ricardomv/temp-humidity-mikrobus/temp-humid.X/src/periph/rtcc.c

/**
  RTCC Generated Driver API Header File

  @Company:
    Microchip Technology Inc.

  @File Name:
    rtcc.c

  @Summary:
    This is the generated header file for the RTCC driver using PIC24 / dsPIC33 / PIC32MM MCUs

  @Description:
    This header file provides APIs for driver for RTCC.
    Generation Information :
        Product Revision  :  PIC24 / dsPIC33 / PIC32MM MCUs - pic24-dspic-pic32mm : 1.75.1
        Device            :  PIC24FJ1024GB610
    The generated drivers are tested against the following:
        Compiler          :  XC16 v1.35
        MPLAB 	          :  MPLAB X v5.05
*/

/*
    (c) 2016 Microchip Technology Inc. and its subsidiaries. You may use this
    software and any derivatives exclusively with Microchip products.

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
    IN NO EVENT WILL MICROCHIP BE LIABLE FOR ANY INDIRECT, SPECIAL, PUNITIVE,
    INCIDENTAL OR CONSEQUENTIAL LOSS, DAMAGE, COST OR EXPENSE OF ANY KIND
    WHATSOEVER RELATED TO THE SOFTWARE, HOWEVER CAUSED, EVEN IF MICROCHIP HAS
    BEEN ADVISED OF THE POSSIBILITY OR THE DAMAGES ARE FORESEEABLE. TO THE
    FULLEST EXTENT ALLOWED BY LAW, MICROCHIP'S TOTAL LIABILITY ON ALL CLAIMS IN
    ANY WAY RELATED TO THIS SOFTWARE WILL NOT EXCEED THE AMOUNT OF FEES, IF ANY,
    THAT YOU HAVE PAID DIRECTLY TO MICROCHIP FOR THIS SOFTWARE.

    MICROCHIP PROVIDES THIS SOFTWARE CONDITIONALLY UPON YOUR ACCEPTANCE OF THESE
    TERMS.
*/


/**
 Section: Included Files
*/

#include <xc.h>
#include "rtcc.h"

/**
// Section: Static function
*/

static void RTCC_Lock(void);
static bool rtccTimeInitialized;
static bool RTCCTimeInitialized(void);
static uint8_t ConvertHexToBCD(uint8_t hexvalue);
static uint8_t ConvertBCDToHex(uint8_t bcdvalue);

void __attribute__ ((weak)) rtcc_alarm_callback(void)
{

}

void __attribute__((__interrupt__, __auto_psv__)) _RTCCInterrupt(void)
{
    rtcc_alarm_callback();
    IFS3bits.RTCIF = 0;   // RTC interrupt flag - clear
}

/**
// Section: Driver Interface Function Definitions
*/

void RTCC_Initialize(void)
{

   RTCCON1Lbits.RTCEN = 0;
   
   __builtin_write_RTCC_WRLOCK();
   
   
   if(!RTCCTimeInitialized())
   {
       // set 2018-11-19 22-29-27
       DATEH = 0x0001;    // Year/Month
       DATEL = 0x0100;    // Date/Wday
       TIMEH = 0x0000;    // hours/minutes
       TIMEL = 0x0000;    // seconds
   }

   // DIV 16383; 
   RTCCON2H = 0x3FFF;

   // Enable RTCC, clear RTCWREN 
   RTCCON1Lbits.RTCEN = 1;  
   RTCC_Lock();

}

static void RTCC_Lock(void)
{
    asm volatile("DISI #6");
    asm volatile("MOV #NVMKEY, W1");
    asm volatile("MOV #0x55, W2");
    asm volatile("MOV W2, [W1]");
    asm volatile("MOV #0xAA, W3");
    asm volatile("MOV W3, [W1]");
    asm volatile("BSET RTCCON1L, #11");
}

bool RTCC_TimeGet(struct tm *currentTime)
{
    uint16_t register_value;
    if(RTCSTATLbits.SYNC){
        return false;
    }

    register_value = DATEH;
    currentTime->tm_year = 100 + ConvertBCDToHex((register_value & 0xFF00) >> 8);
    currentTime->tm_mon = ConvertBCDToHex(register_value & 0x00FF) - 1;
    
    register_value = DATEL;
    currentTime->tm_mday = ConvertBCDToHex((register_value & 0xFF00) >> 8);
    currentTime->tm_wday = ConvertBCDToHex(register_value & 0x00FF);
    
    register_value = TIMEH;
    currentTime->tm_hour = ConvertBCDToHex((register_value & 0xFF00) >> 8);
    currentTime->tm_min = ConvertBCDToHex(register_value & 0x00FF);
    
    register_value = TIMEL;
    currentTime->tm_sec = ConvertBCDToHex((register_value & 0xFF00) >> 8);
   
    return true;
}

void RTCC_TimeSet(struct tm *initialTime)
{

  __builtin_write_RTCC_WRLOCK();

   RTCCON1Lbits.RTCEN = 0;
   

   // set RTCC initial time
   DATEH = (ConvertHexToBCD(initialTime->tm_year - 100) << 8) | ConvertHexToBCD(initialTime->tm_mon + 1) ;  // YEAR/MONTH-1
   DATEL = (ConvertHexToBCD(initialTime->tm_mday) << 8) | ConvertHexToBCD(initialTime->tm_wday) ;  // /DAY-1/WEEKDAY
   TIMEH = (ConvertHexToBCD(initialTime->tm_hour) << 8)  | ConvertHexToBCD(initialTime->tm_min); // /HOURS/MINUTES
   TIMEL = (ConvertHexToBCD(initialTime->tm_sec) << 8) ;   // SECOND
           
   // Enable RTCC, clear RTCWREN         
   RTCCON1Lbits.RTCEN = 1;  
   RTCC_Lock();

}

void RTCC_AlarmSet(struct tm *alarmTime, enum RTCC_REPEAT mask, unsigned int counter, unsigned int chime)
{
    RTCCON1Hbits.ALRMEN = 0;     // Disable alarm to avoid a false alarm event

    if(alarmTime == NULL) {
        ALMDATEH = 0;
        ALMDATEL = 0;
        ALMTIMEH = 0;
        ALMTIMEL = 0;
    } else {
        ALMDATEH = (ConvertHexToBCD(alarmTime->tm_year - 100) << 8) | ConvertHexToBCD(alarmTime->tm_mon + 1) ;  // YEAR/MONTH-1
        ALMDATEL = (ConvertHexToBCD(alarmTime->tm_mday) << 8) | ConvertHexToBCD(alarmTime->tm_wday) ;  // /DAY-1/WEEKDAY
        ALMTIMEH = (ConvertHexToBCD(alarmTime->tm_hour) << 8)  | ConvertHexToBCD(alarmTime->tm_min); // /HOURS/MINUTES
        ALMTIMEL = (ConvertHexToBCD(alarmTime->tm_sec) << 8) ;   // SECOND
    }

    RTCCON1Hbits.AMASK = mask;      // Repetition
    RTCCON1Hbits.ALMRPT = counter;  // Repeat # times
    RTCCON1Hbits.CHIME = chime;         // Roll over ALMRPT
    RTCCON1Hbits.ALRMEN = 1;        // Enable alarm
}

bool RTCC_BCDTimeGet(bcdTime_t *currentTime)
{
    uint16_t register_value;
    if(RTCSTATLbits.SYNC){
        return false;
    }
   
    register_value = DATEH;
    currentTime->tm_year = (register_value & 0xFF00) >> 8;
    currentTime->tm_mon = register_value & 0x00FF;
    
    register_value = DATEL;
    currentTime->tm_mday = (register_value & 0xFF00) >> 8;
    currentTime->tm_wday = register_value & 0x00FF;
    
    register_value = TIMEH;
    currentTime->tm_hour = (register_value & 0xFF00) >> 8;
    currentTime->tm_min = register_value & 0x00FF;
   
    register_value = TIMEL;
    currentTime->tm_sec = (register_value & 0xFF00) >> 8;

    return true;
}

void RTCC_BCDTimeSet(bcdTime_t *initialTime)
{

   __builtin_write_RTCC_WRLOCK();

   RTCCON1Lbits.RTCEN = 0;
   

   // set RTCC initial time
   DATEH = (initialTime->tm_year << 8) | (initialTime->tm_mon) ;  // YEAR/MONTH-1
   DATEL = (initialTime->tm_mday << 8) | (initialTime->tm_wday) ;  // /DAY-1/WEEKDAY
   TIMEH = (initialTime->tm_hour << 8) | (initialTime->tm_min); // /HOURS/MINUTES
   TIMEL = (initialTime->tm_sec << 8);   // SECONDS   
           
   // Enable RTCC, clear RTCWREN         
   RTCCON1Lbits.RTCEN = 1;  
   RTCC_Lock();

}

/**
 This function implements RTCC_TimeReset.This function is used to
 used by application to reset the RTCC value and reinitialize RTCC value.
*/
void RTCC_TimeReset(bool reset)
{
    rtccTimeInitialized = reset;
}

static bool RTCCTimeInitialized(void)
{
    return(rtccTimeInitialized);
}

void RTCC_TimestampAEventManualSet(void)
{
    RTCSTATLbits.TSAEVT = 1;
}

bool RTCC_TimestampADataGet(struct tm *currentTime)
{
    uint16_t register_value;
    if(!RTCSTATLbits.TSAEVT){
        return false;
    }
  
    register_value = TSADATEH;
    currentTime->tm_year = 100 + ConvertBCDToHex((register_value & 0xFF00) >> 8);
    currentTime->tm_mon = ConvertBCDToHex(register_value & 0x00FF) - 1;
    
    register_value = TSADATEL;
    currentTime->tm_mday = ConvertBCDToHex((register_value & 0xFF00) >> 8);
    currentTime->tm_wday = ConvertBCDToHex(register_value & 0x00FF);
    
    register_value = TSATIMEH;
    currentTime->tm_hour = ConvertBCDToHex((register_value & 0xFF00) >> 8);
    currentTime->tm_min = ConvertBCDToHex(register_value & 0x00FF);
    
    register_value = TSATIMEL;
    currentTime->tm_sec = ConvertBCDToHex((register_value & 0xFF00) >> 8);
   
    RTCSTATLbits.TSAEVT = 0;

    return true;
}



bool RTCC_TimestampA_BCDDataGet(bcdTime_t *currentTime)
{
    uint16_t register_value;
    if(!RTCSTATLbits.TSAEVT){
        return false;
    }
  
    register_value = TSADATEH;
    currentTime->tm_year = (register_value & 0xFF00) >> 8;
    currentTime->tm_mon = (register_value & 0x00FF);
    
    register_value = TSADATEL;
    currentTime->tm_mday = (register_value & 0xFF00) >> 8;
    currentTime->tm_wday = (register_value & 0x00FF);
    
    register_value = TSATIMEH;
    currentTime->tm_hour = (register_value & 0xFF00) >> 8;
    currentTime->tm_min = (register_value & 0x00FF);
    
    register_value = TSATIMEL;
    currentTime->tm_sec = (register_value & 0xFF00) >> 8;
   
    RTCSTATLbits.TSAEVT = 0;

    return true;
}



static uint8_t ConvertHexToBCD(uint8_t hexvalue)
{
    uint8_t bcdvalue;
    bcdvalue = (hexvalue / 10) << 4;
    bcdvalue = bcdvalue | (hexvalue % 10);
    return (bcdvalue);
}

static uint8_t ConvertBCDToHex(uint8_t bcdvalue)
{
    uint8_t hexvalue;
    hexvalue = (((bcdvalue & 0xF0) >> 4)* 10) + (bcdvalue & 0x0F);
    return hexvalue;
}


/* Function:
    bool RTCC_Task(void)

  Summary:
    Status function which returns the RTCC interrupt flag status

  Description:
    This is the status function for the RTCC peripheral. 
*/
bool RTCC_Task(void)
{
    bool status;
    status = IFS3bits.RTCIF;
    if( IFS3bits.RTCIF)
    {
       IFS3bits.RTCIF = false;
    }
    return status;
}
/**
 End of File
*/
