ricardomv/temp-humidity-mikrobus/temp-humid.X/src/periph/timer.c

/*
 * Copyright (C) 2017  Francois Berder <fberder@outlook.fr>
 *
 * This file is part of pic24-framework.
 *
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
 * You should have received a copy of the GNU General Public License
 * along with pic24-framework.  If not, see <http://www.gnu.org/licenses/>.
 */

#include <xc.h>
#include "mcu.h"
#include "timer.h"
#include "periph_conf.h"

void __attribute__ ((weak)) timer2_callback(void)
{

}

void __attribute__ ((weak)) timer3_callback(void)
{

}

void __attribute__ ((weak)) timer4_callback(void)
{

}

void __attribute__ ((weak)) timer5_callback(void)
{

}

void __attribute__ ((interrupt, no_auto_psv)) _T2Interrupt(void)
{
    timer2_callback();
    IFS0 &= ~ _IFS0_T2IF_MASK;
}

void __attribute__ ((interrupt, no_auto_psv)) _T3Interrupt(void)
{
    timer3_callback();
    IFS0 &= ~ _IFS0_T3IF_MASK;
}

void __attribute__ ((interrupt, no_auto_psv)) _T4Interrupt(void)
{
    timer4_callback();
    IFS1 &= ~ _IFS1_T4IF_MASK;
}

void __attribute__ ((interrupt, no_auto_psv)) _T5Interrupt(void)
{
    timer5_callback();
    IFS1 &= ~ _IFS1_T5IF_MASK;
}

void timer_configure(unsigned int timer_num,
                     uint8_t prescaler, uint16_t period,
                     uint8_t enable_interrupt)
{
    switch (timer_num) {
    case TIMER_2:
        T2CON = (prescaler << _T2CON_TCKPS_POSITION) & _T2CON_TCKPS_MASK;
        PR2 = period;
        TMR2 = 0;
        IFS0 &= ~ _IFS0_T2IF_MASK;
        break;
    case TIMER_3:
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
    switch (timer_num) {
    case TIMER_2:
        PMD1 |= _PMD1_T2MD_MASK;
        break;
    case TIMER_3:
        PMD1 |= _PMD1_T3MD_MASK;
        break;
    case TIMER_4:
        PMD1 |= _PMD1_T4MD_MASK;
        break;
    case TIMER_5:
        PMD1 |= _PMD1_T5MD_MASK;
        break;
    }
}
