ricardomv/temp-humidity-mikrobus/temp-humid.X/src/explorer1632.h

#ifndef __EXPLORER1632_H__
#define __EXPLORER1632_H__

#define LED_D3_PIN            GPIO_PIN(PORT_A, 0)
#define LED_D4_PIN            GPIO_PIN(PORT_A, 1)
#define LED_D5_PIN            GPIO_PIN(PORT_A, 2)
#define LED_D6_PIN            GPIO_PIN(PORT_A, 3)
#define LED_D7_PIN            GPIO_PIN(PORT_A, 4)
#define LED_D8_PIN            GPIO_PIN(PORT_A, 5)
#define LED_D9_PIN            GPIO_PIN(PORT_A, 6)
#define LED_D10_PIN           GPIO_PIN(PORT_A, 7)

#define BUTTON_S3_PIN         GPIO_PIN(PORT_D, 6)
#define BUTTON_S4_PIN         GPIO_PIN(PORT_D, 13)
#define BUTTON_S5_PIN         LED_D10_PIN
#define BUTTON_S6_PIN         GPIO_PIN(PORT_D, 7)

#endif /* __EXPLORER1632_H__ */
