ricardomv/temp-humidity-mikrobus/temp-humid.X/src/drivers/sdcard_cache.h

/*
 * Copyright (C) 2017  Francois Berder <fberder@outlook.fr>
 *
 * This file is part of pic24-framework.
 *
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
 * You should have received a copy of the GNU General Public License
 * along with pic24-framework.  If not, see <http://www.gnu.org/licenses/>.
 */

#ifndef __BLOCK_STORAGE_H__
#define __BLOCK_STORAGE_H__

#include <stdint.h>
#include "sdcard.h"

/** Keep various information about cache behavior */
struct sdcard_cache_stats_t {
    uint32_t evictions;         /**< Number of evictions from cache */
    uint32_t write_success;     /**< Number of successful writes */
    uint32_t read_success;      /**< Number of successful reads */
    uint32_t write_error;       /**< Number of erroneous writes */
    uint32_t read_error;        /**< Number of erroneous reads */
};

/**
 * @brief Initialise SD card cache
 *
 * This function does not configure the SD card. It is assumed
 * that it has already been done before.
 * The current address is set to 0.
 *
 * The device given as an argument will be used in all following
 * calls.
 *
 * @param[in] dev
 */
void sdcard_cache_init(struct sdcard_spi_dev_t dev);

/**
 * @brief Read bytes from block storage at current address
 *
 * @param[out] buffer
 * @param[in] length Number of bytes to read
 */
int sdcard_cache_read(void *buffer, uint32_t length);

/**
 * @brief Read one byte from block storage at current address
 *
 * @param[in] data
 */
int sdcard_cache_read_byte(void *data);

/**
 * @brief Write bytes to block storage at current address
 *
 * @param[in] buffer
 * @param[in] length Number of bytes to write
 */
int sdcard_cache_write(const void *buffer, uint32_t length);

/**
 * @brief Set the current address
 *
 * @param[in] address
 */
int sdcard_cache_seek(uint32_t address);

/**
 * @brief Flush all dirty blocks to the SD card
 *
 * Reset all counters.
 * This function should be called from time to time to
 * ensure that:
 *   - data is written back to the SD card
 *   - cache entry eviction works in an optimal fashion
 */
void sdcard_cache_flush(void);

/**
 * @return Statistics of the SD card cache
 */
struct sdcard_cache_stats_t sdcard_cache_get_stats(void);

#endif
